rursprung/fhgr-mrproj2/smt_gun_controller/src/smt_gun_controller_node.cpp

#include <ros/ros.h>

#include "smt_gun_controller/gun_controller.hpp"

int main(int argc, char** argv) {
    ros::init(argc, argv, "smt_gun_controller");
    ros::NodeHandle nodeHandle("~");

    smt::gun_controller::GunController gunController(nodeHandle);

    ros::spin();
    return 0;
}
